marekw1986/RetroEG/code/mc6840.c

#include <6502.h>
#include <stdlib.h>
#include <string.h>
#include "modbus.h"
#include "mc6840.h"

volatile uint32_t milliseconds = 0;
volatile uint32_t uptime_value = 0;
volatile uint8_t  geiger_ind = 0;
volatile uint16_t geiger_pulses[60];


char* __fastcall__ utoa (unsigned val, char* buf, int radix);
char* __fastcall__ strcat (char* s1, const char* s2);


void mc6840_init (void) {
	uint8_t i;
	
    MC6840_CON13 = TM_COUNTER_OUTPUT_DISABLE | TM_INTERUPT_ENABLE | TM_CONT_OP_MODE1 | TM_NORMAL_16BIT | TM_SYS_CLK | TMCR3_T3_CLK_NO_PRESCALER;	//CON3 first by default after reset. TIMER3 is used for systick. Output diable and sys clk.
    MC6840_CON2 = TM_COUNTER_OUTPUT_ENABLE | TM_INTERUPT_DISABLE | TM_CONT_OP_MODE1 | TM_NORMAL_16BIT | TM_SYS_CLK | TMCR2_WRITE_CR1;				//CON2 accessed directly. TIMER2 generates sound. Output enable and sys clk.
    MC6840_CON13 = TM_COUNTER_OUTPUT_DISABLE | TM_INTERUPT_DISABLE | TM_CONT_OP_MODE1 | TM_NORMAL_16BIT | TM_EXT_CLK | TMCR1_ALL_TIMERS_ALLOWED;	//CON1. TIMER1 counts Geiger pulses, so external source
    MC6840_TIMER1 = Swap2Bytes(0xFFFF);       //Remember about endianess - MC6800 family is big endian, 6502 is little endian. Remember that timer is decremented.
    MC6840_TIMER2 = Swap2Bytes(0xF82F);       //500 Hz signal on audio output
    MC6840_TIMER3 = Swap2Bytes(0x03E7);       //1ms interrupt (0xFFFF - 10000) - it is decremented!
    
    for (i=0; i<60; i++) geiger_pulses[i] = 0x00;
}


uint16_t millis(void) {
	uint16_t tmp;
    SEI();
    tmp = milliseconds;
    CLI();
	return tmp;
}

uint32_t uptime (void) {
	uint32_t tmp;
	SEI();
	tmp = uptime_value;
	CLI();
	return tmp;
}


uint16_t get_geiger_pulses (void) {
	uint8_t i;
	uint16_t cpm = 0;
	
	SEI();
	for (i=0; i<60; i++) cpm += geiger_pulses[i];
	CLI();
    return cpm;
}


char* get_usiv_str (char * des) {
	volatile uint16_t* siv;
	char buffer[16];
	
	des[0] = '\0';
	//siv = GEIGER_USV(cpmin);
	//integer = siv/10000;
	//fraction = siv%10000;
	siv = modbus_get_sivert();
	utoa(siv[0], buffer, 10);
	strcat(des, buffer);
	strcat(des, ".");
	if (siv[1] < 1000) {
		strcat(des, "0");
		if (siv[1] < 100) {
			strcat(des, "0");
			if (siv[1] < 10) {
				strcat(des, "0");
			}
		}
	}
	utoa(siv[1], buffer, 10);
	strcat(des, buffer);
	return des;	
}


void set_sound_frequency (uint16_t freq) {
    if (freq < 24) return;          //Min required frequency. It will solve div/0 and word size issues.
    MC6840_TIMER2 = Swap2Bytes(0xFFFF-(1000000/freq));
}
